virtualabs/lehack26-badge/firmware/qrcode.hpp

#define QRCODE_WIDTH 127  // logo width
#define QRCODE_HEIGHT 127  // logo height
PROGMEM const unsigned char badge_qrcode[] = {
  0x00, 0x00, 0x00, 0x00, 0x00, 0x00, 0x00, 0x00, 0x00, 0x00, 0x00, 0x00, 
  0x00, 0x00, 0x00, 0x00, 0x00, 0x00, 0x00, 0x00, 0x00, 0x00, 0x00, 0x00, 
  0x00, 0x00, 0x00, 0x00, 0x00, 0x00, 0x00, 0x00, 0xFC, 0xFF, 0x7F, 0xFC, 
  0xC0, 0x8F, 0xE3, 0xC7, 0xFF, 0xFF, 0x3F, 0x70, 0x1C, 0xFF, 0xFF, 0x1F, 
  0xFC, 0xFF, 0x7F, 0xFC, 0xC0, 0x8F, 0xE3, 0xC7, 0xFF, 0xFF, 0x3F, 0x70, 
  0x1C, 0xFF, 0xFF, 0x1F, 0xFC, 0xFF, 0x7F, 0xFC, 0xC0, 0x8F, 0xE3, 0xC7, 
  0xFF, 0xFF, 0x3F, 0x70, 0x1C, 0xFF, 0xFF, 0x1F, 0x1C, 0x00, 0x70, 0x00, 
  0xF8, 0xFF, 0xE3, 0xF8, 0x7F, 0x1C, 0x00, 0x0E, 0x1C, 0x07, 0x00, 0x1C, 
  0x1C, 0x00, 0x70, 0x00, 0xF8, 0xFF, 0xE3, 0xF8, 0x7F, 0x1C, 0x00, 0x0E, 
  0x1C, 0x07, 0x00, 0x1C, 0x1C, 0x00, 0x70, 0x00, 0xF8, 0xFF, 0xE3, 0xF8, 
  0x7F, 0x1C, 0x00, 0x0E, 0x1C, 0x07, 0x00, 0x1C, 0x1C, 0xFF, 0x71, 0x1C, 
  0x00, 0x0E, 0x1C, 0xF8, 0x81, 0x03, 0xC7, 0xFF, 0x03, 0xC7, 0x7F, 0x1C, 
  0x1C, 0xFF, 0x71, 0x1C, 0x00, 0x0E, 0x1C, 0xF8, 0x81, 0x03, 0xC7, 0xFF, 
  0x03, 0xC7, 0x7F, 0x1C, 0x1C, 0xFF, 0x71, 0x1C, 0x00, 0x0E, 0x1C, 0xF8, 
  0x81, 0x03, 0xC7, 0xFF, 0x03, 0xC7, 0x7F, 0x1C, 0x1C, 0xFF, 0x71, 0xE0, 
  0x38, 0x80, 0x1F, 0x38, 0x0E, 0x1C, 0x07, 0x00, 0x1C, 0xC7, 0x7F, 0x1C, 
  0x1C, 0xFF, 0x71, 0xE0, 0x38, 0x80, 0x1F, 0x38, 0x0E, 0x1C, 0x07, 0x00, 
  0x1C, 0xC7, 0x7F, 0x1C, 0x1C, 0xFF, 0x71, 0xE0, 0x38, 0x80, 0x1F, 0x38, 
  0x0E, 0x1C, 0x07, 0x00, 0x1C, 0xC7, 0x7F, 0x1C, 0x1C, 0xFF, 0x71, 0x1C, 
  0x38, 0x00, 0xE0, 0x38, 0x80, 0xE3, 0x3F, 0xF0, 0x03, 0xC7, 0x7F, 0x1C, 
  0x1C, 0xFF, 0x71, 0x1C, 0x38, 0x00, 0xE0, 0x38, 0x80, 0xE3, 0x3F, 0xF0, 
  0x03, 0xC7, 0x7F, 0x1C, 0x1C, 0xFF, 0x71, 0x1C, 0x38, 0x00, 0xE0, 0x38, 
  0x80, 0xE3, 0x3F, 0xF0, 0x03, 0xC7, 0x7F, 0x1C, 0x1C, 0x00, 0x70, 0x00, 
  0xC7, 0x7F, 0x00, 0x00, 0x7E, 0xE0, 0x00, 0x7E, 0x1C, 0x07, 0x00, 0x1C, 
  0x1C, 0x00, 0x70, 0x00, 0xC7, 0x7F, 0x00, 0x00, 0x7E, 0xE0, 0x00, 0x7E, 
  0x1C, 0x07, 0x00, 0x1C, 0x1C, 0x00, 0x70, 0x00, 0xC7, 0x7F, 0x00, 0x00, 
  0x7E, 0xE0, 0x00, 0x7E, 0x1C, 0x07, 0x00, 0x1C, 0xFC, 0xFF, 0x7F, 0x1C, 
  0xC7, 0x71, 0x1C, 0xC7, 0x71, 0x1C, 0xC7, 0x71, 0x1C, 0xFF, 0xFF, 0x1F, 
  0xFC, 0xFF, 0x7F, 0x1C, 0xC7, 0x71, 0x1C, 0xC7, 0x71, 0x1C, 0xC7, 0x71, 
  0x1C, 0xFF, 0xFF, 0x1F, 0xFC, 0xFF, 0x7F, 0x1C, 0xC7, 0x71, 0x1C, 0xC7, 
  0x71, 0x1C, 0xC7, 0x71, 0x1C, 0xFF, 0xFF, 0x1F, 0x00, 0x00, 0x00, 0xFC, 
  0xC7, 0x0F, 0x1C, 0xC0, 0x8F, 0x03, 0xFF, 0xFF, 0x1F, 0x00, 0x00, 0x00, 
  0x00, 0x00, 0x00, 0xFC, 0xC7, 0x0F, 0x1C, 0xC0, 0x8F, 0x03, 0xFF, 0xFF, 
  0x1F, 0x00, 0x00, 0x00, 0x00, 0x00, 0x00, 0xFC, 0xC7, 0x0F, 0x1C, 0xC0, 
  0x8F, 0x03, 0xFF, 0xFF, 0x1F, 0x00, 0x00, 0x00, 0x00, 0x00, 0x7E, 0x00, 
  0xFF, 0x01, 0x00, 0xC0, 0xFF, 0xFF, 0x38, 0x0E, 0x1C, 0xC7, 0x71, 0x1C, 
  0x00, 0x00, 0x7E, 0x00, 0xFF, 0x01, 0x00, 0xC0, 0xFF, 0xFF, 0x38, 0x0E, 
  0x1C, 0xC7, 0x71, 0x1C, 0x00, 0x00, 0x7E, 0x00, 0xFF, 0x01, 0x00, 0xC0, 
  0xFF, 0xFF, 0x38, 0x0E, 0x1C, 0xC7, 0x71, 0x1C, 0x00, 0x38, 0x00, 0x1C, 
  0x38, 0x8E, 0x1F, 0x38, 0x00, 0xE0, 0xC7, 0x81, 0x03, 0x07, 0xF0, 0x1F, 
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
