virtualabs/lehack26-badge/firmware/face.cpp

#include "face.hpp"

/**
 * Initialize an Eye object on screen at position (x,y).
 */

Eye::Eye(EyeSide side, int x, int y, uint16_t bgColor) {
  m_side = side;
  m_x = x;
  m_y = y;
  m_w = EYE_W;
  m_h = EYE_H;
  m_bgColor = bgColor;
}


/**
 * Initialize an Eye object on screen at position (x,y) of size (w,h).
 */
 
Eye::Eye(EyeSide side, int x, int y, int w, int h, uint16_t bgColor) {
  m_side = side;
  m_x = x;
  m_y = y;
  m_w = w;
  m_h = h;
  m_bgColor = bgColor;
}

/**
 * Destructor.
 */
Eye::~Eye() {
}

/**
 * Getters.
 */
int Eye::x(void) {
  return m_x;
}

int Eye::y(void) {
  return m_y;
}

int Eye::w(void) {
  return m_w;
}

int Eye::h(void) {
  return m_h;
}

void Eye::update(int x, int y, int w, int h) {
  m_x = x;
  m_y = y;
  m_w = w;
  m_h = h;
}

void Eye::setBgColor(uint16_t color) {
  m_bgColor = color;
}

/**
 * Draws the eye on screen.
 */

void Eye::draw(TFT_eSprite &screen) {
  int h = m_h - 20*abs(m_x - 120)/120;

  if (m_h < 35) {
    switch (m_side) {
      case EyeSide::LEFT:
        screen.drawWideLine(m_x + m_w/2 - 20, m_y - h/2 - 5, m_x + m_w - 4, m_y - h/2, 6, TFT_WHITE, m_bgColor);
        break;

      case EyeSide::RIGHT:
        screen.drawWideLine(m_x + m_w/2 + 20, m_y - h/2 - 5, m_x + 4, m_y - h/2, 6, TFT_WHITE, m_bgColor);
        break;
    }
    screen.fillRoundRect(m_x, m_y - h/2, m_w, h, 2, TFT_WHITE);
  } else {
    screen.fillSmoothRoundRect(m_x, m_y - h/2, m_w, h, 10, TFT_WHITE, m_bgColor);
  }
}

/***********************
 * Mouth
 **********************/

Mouth::Mouth(int x, int y, int w, int z) : m_x(x), m_y(y), m_w(w), m_z(z)
{
}

Mouth::~Mouth()
{
}

int Mouth::x(void)
{
  return m_x;
}

int Mouth::y(void)
{
  return m_y;
}

int Mouth::w(void)
{
  return m_w;
}

int Mouth::z(void)
{
  return m_z;
}

void Mouth::update(int x, int y, int w, int z)
{
  m_x = x;
  m_y = y;
  m_w = w;
  m_z = z;
}

void Mouth::draw(TFT_eSprite &screen)
{
  int x = 15 + ((m_x*210)/240);
  int w = m_w - 20*abs(m_x - 120)/120;
  int y = m_y - 10*abs(m_x - 120)/120;
  screen.drawWideLine(x - w/2 - 10, y - m_z, x - w/2, y, 10, TFT_WHITE, TFT_WHITE);
  screen.drawWideLine(x + w/2, y, x + w/2 + 10, y - m_z, 10, TFT_WHITE, TFT_WHITE);
  screen.drawWideLine(x - w/2, y, x + w/2, y, 10, TFT_WHITE, TFT_WHITE);
}

/***********************
 * Face management.
 ***********************/

PalFace::PalFace(uint16_t bgColor) : m_right_eye(EyeSide::RIGHT, EYE_RIGHT_DEF_X, EYE_RIGHT_DEF_Y, TFT_SKYBLUE), m_left_eye(EyeSide::LEFT, EYE_LEFT_DEF_X, EYE_LEFT_DEF_Y, TFT_SKYBLUE),
  m_mouth(MOUTH_X, MOUTH_Y, MOUTH_W, MOUTH_Z), m_bgColor(bgColor)
{
}

PalFace::~PalFace() {

}

void PalFace::moveEyes(int x, int y) {
  m_right_eye.update(x + EYE_SPACING/2, y - m_right_eye.h()/2, m_right_eye.w(), m_right_eye.h());
  m_left_eye.update(x - EYE_SPACING/2 - m_left_eye.w(), y - m_left_eye.h()/2, m_left_eye.w(), m_left_eye.h());
}

void PalFace::moveMouth(int x, int y, int z) {
  m_mouth.update(x, y, m_mouth.w(), z);
}

void PalFace::changeEyes(int w, int h) {
  m_right_eye.update(m_right_eye.x(), m_right_eye.y(), w, h);
  m_left_eye.update(m_left_eye.x(), m_left_eye.y(), w, h);
}

void PalFace::setBgColor(uint16_t color) {
  m_bgColor = color;
  m_right_eye.setBgColor(color);
  m_left_eye.setBgColor(color);
}

void PalFace::draw(TFT_eSprite &screen) {
  screen.fillScreen(m_bgColor);
  m_left_eye.draw(screen);
  m_right_eye.draw(screen);
  m_mouth.draw(screen);
}
